Deni90/singleDigitNixieClock/firmware/include/In18NixieTube.h

#pragma once

#include "BCD2DecimalDecoder.h"
#include <inttypes.h>

class In18NixieTube {
  private:
    BCD2DecimalDecoder& decoder;

  public:
    In18NixieTube(BCD2DecimalDecoder& decoder);
    void Initialize();
    void ShowDigit(uint8_t digit);
    void HideDigit();
};
